JINMING2333/casa0014/images/data2.png

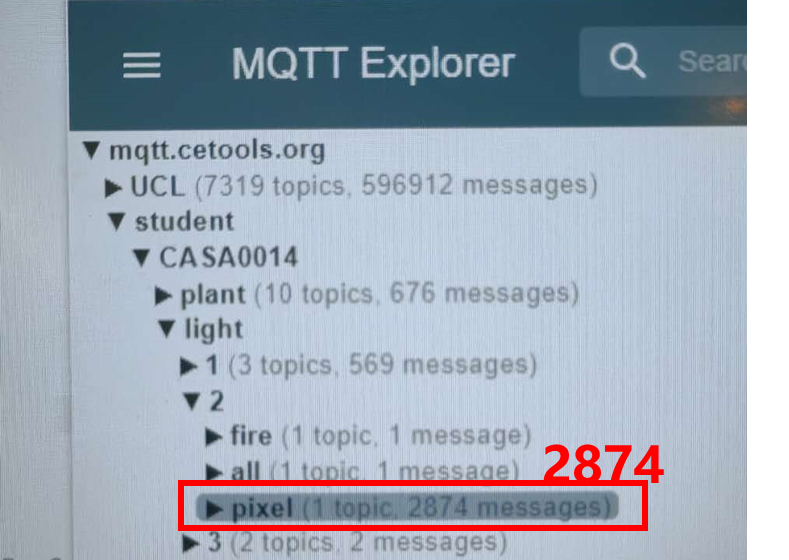
images/data2.png
