JINMING2333/casa0014/images/enclosure1.jpg

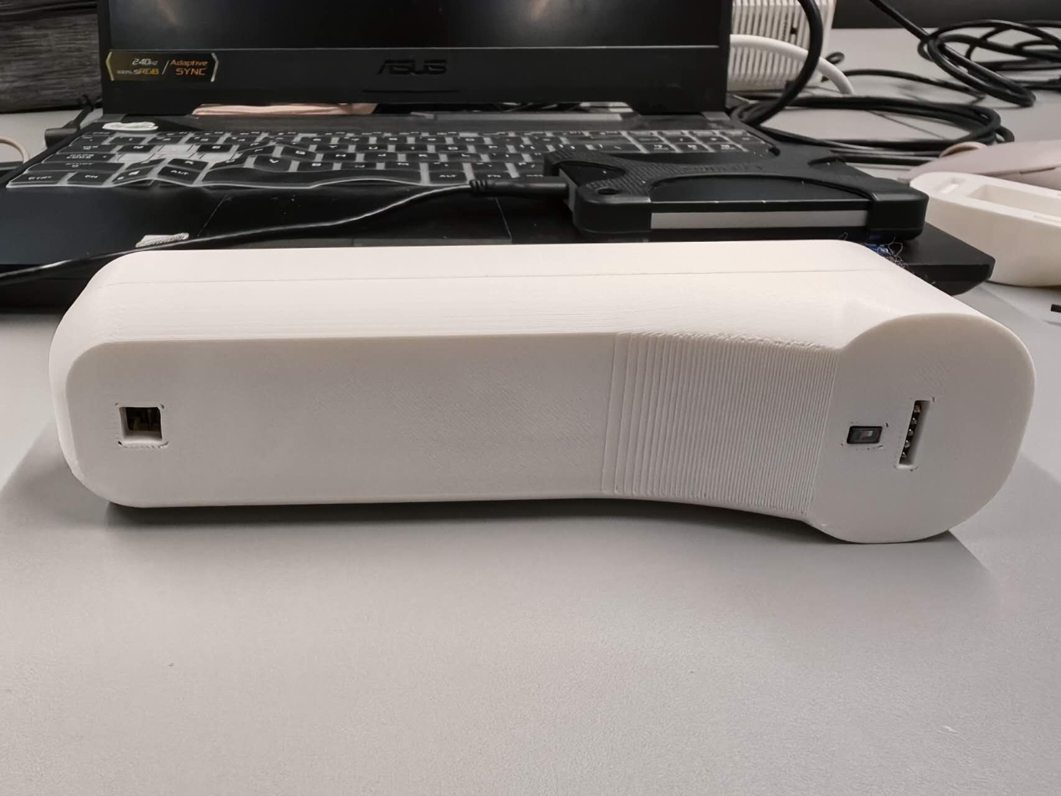
images/enclosure1.jpg
