JINMING2333/casa0014/images/enclosure2.jpg

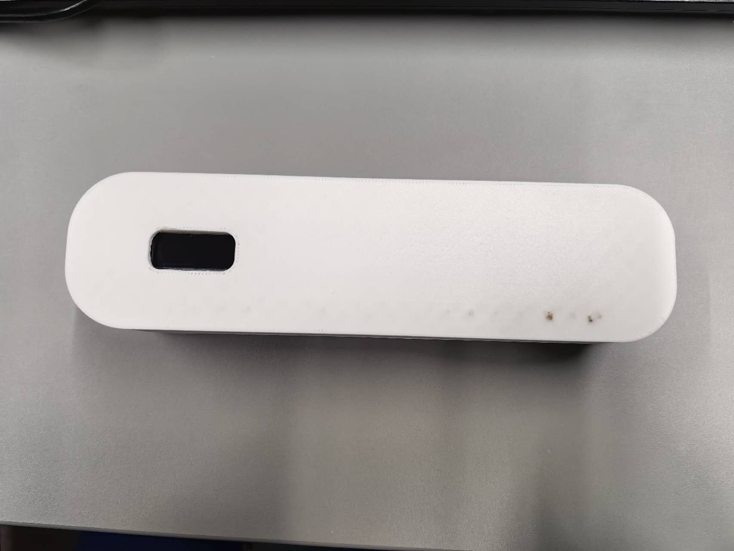
images/enclosure2.jpg
