JINMING2333/casa0014/images/final_play.png

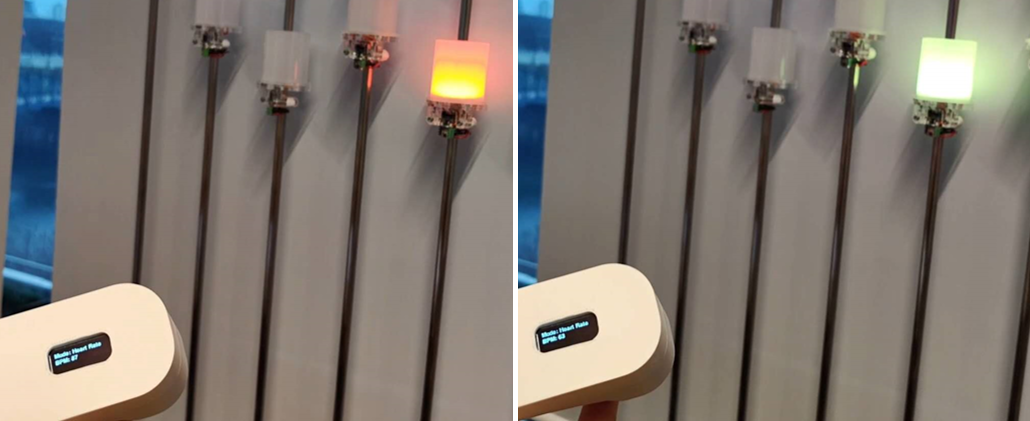
images/final_play.png
